Global-Health-Engineering/plastic-scanner/Images/initial_UI.jpeg

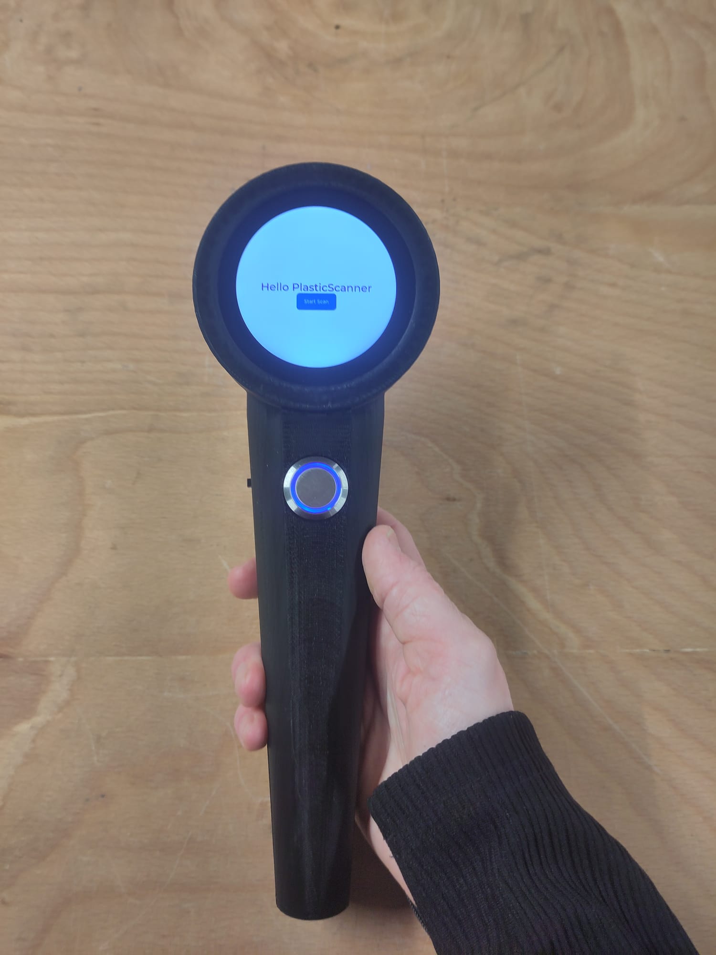
Images/initial_UI.jpeg
