Global-Health-Engineering/plastic-scanner/Images/scanning.jpeg

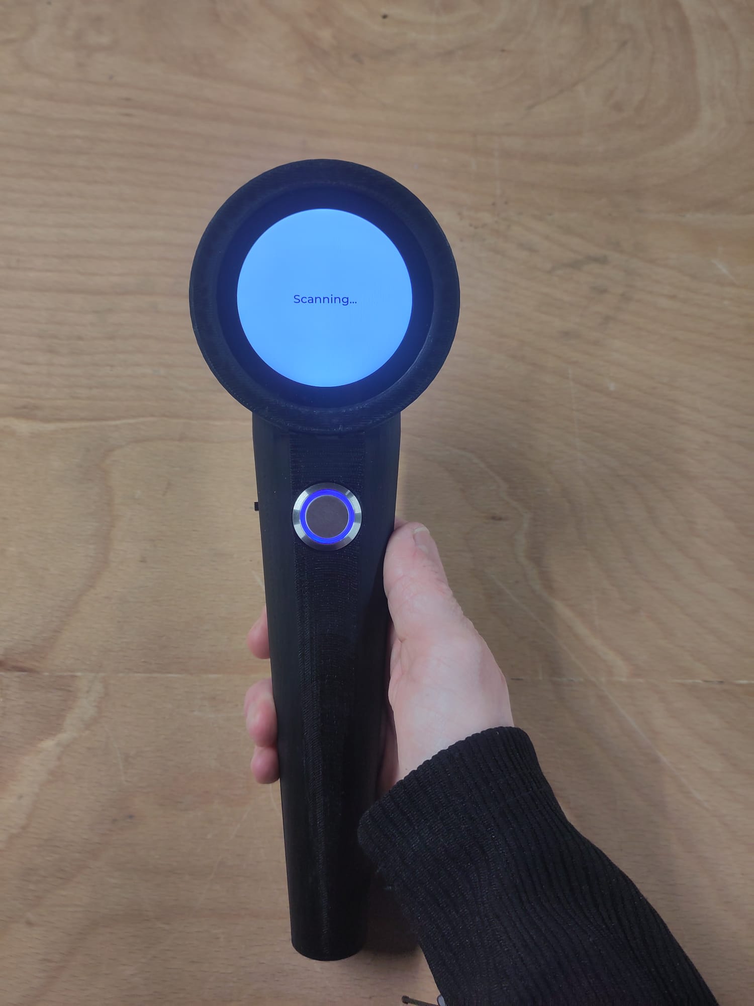
Images/scanning.jpeg
