Global-Health-Engineering/plastic-scanner/Images/WhatsApp Image 2026-01-21 at 16.56.18.jpeg

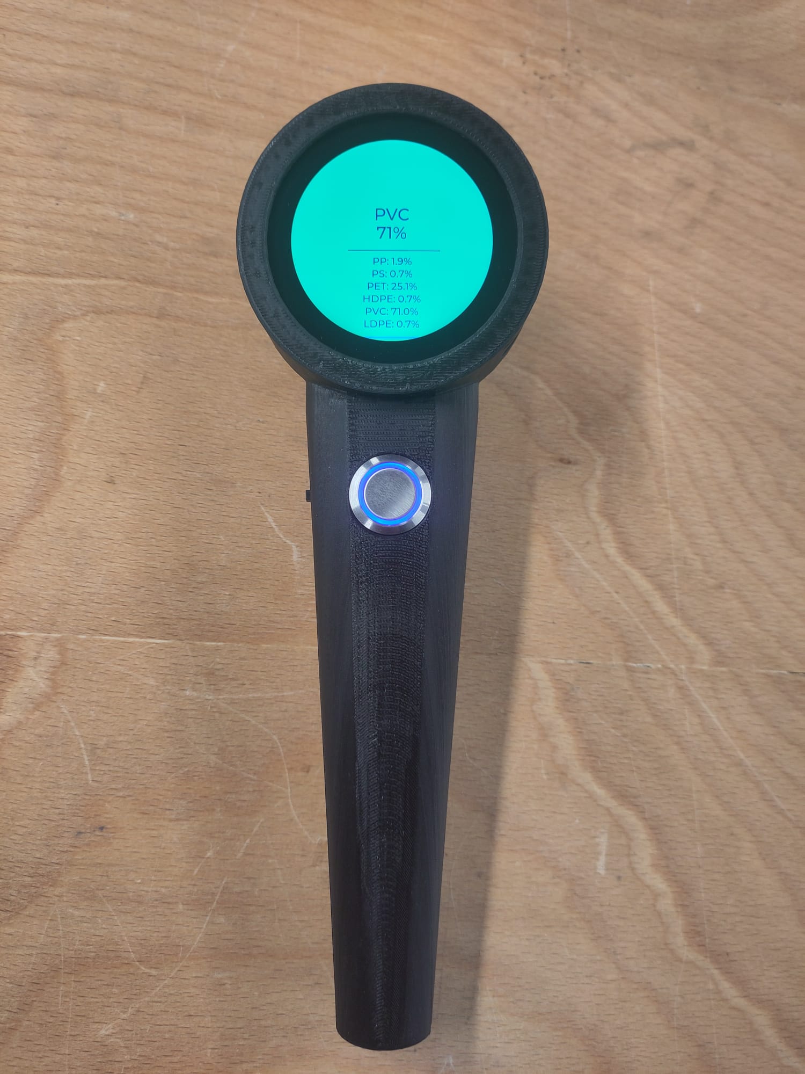
Images/WhatsApp Image 2026-01-21 at 16.56.18.jpeg
