Global-Health-Engineering/plastic-scanner/CAD/STEP files/low_shell_angle.STEP

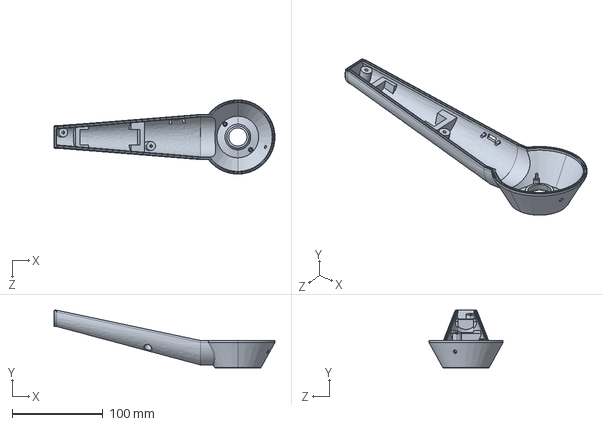
[picture p45: CAD file, 2026-01-22]
CAD/STEP files/low_shell_angle.STEP
244.0 x 63.5 x 82.0 mm
