Global-Health-Engineering/plastic-scanner/CAD/STEP files/fixture_LCD.STEP

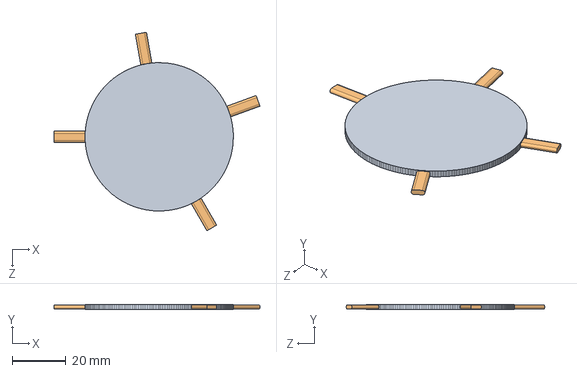
[picture p46: CAD file, 2026-01-22]
CAD/STEP files/fixture_LCD.STEP
76.4 x 2.00 x 73.6 mm
