Global-Health-Engineering/plastic-scanner/Hardware/Scanning PCB/RoundScanner_Ki_CAD_files/3dmodels/Diodes_Inc._-_BSS138DW-7-F 2.step

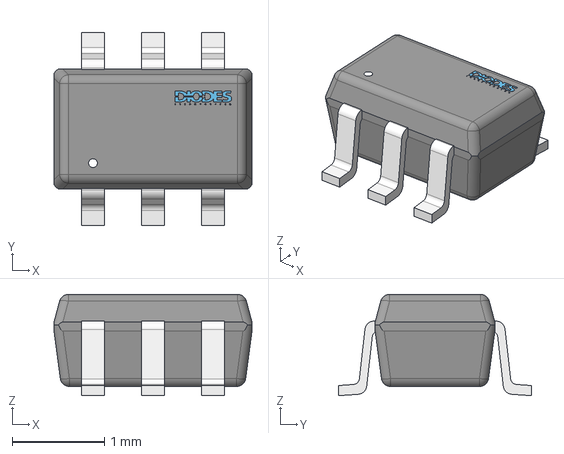
[picture p47: CAD file, 2026-01-18]
Hardware/Scanning PCB/RoundScanner_Ki_CAD_files/3dmodels/Diodes_Inc._-_BSS138DW-7-F 2.step
2.15 x 2.10 x 1.10 mm
