Global-Health-Engineering/plastic-scanner/Firmware/Firmware Handheld Plastic Scanner LilyGo/dimensions/T-RGB-PCB.DXF

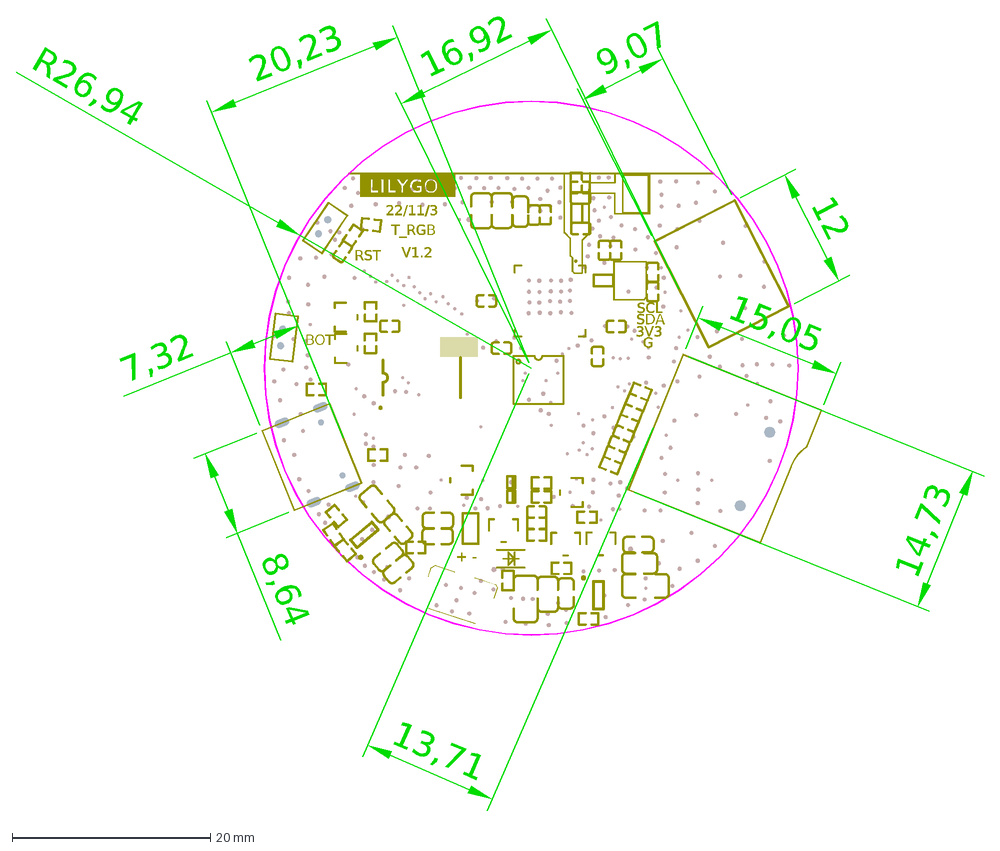
[picture p48: CAD file, 2026-01-21]
Firmware/Firmware Handheld Plastic Scanner LilyGo/dimensions/T-RGB-PCB.DXF
22/11/3
V1.2
T_RGB
3V3
SDA
SCL
G
-
+
BOT
RST
R26,94
13,71
20,23
16,92
12
9,07
15,05
14,73
8,64
7,32
