Global-Health-Engineering/plastic-scanner/Hardware/Scanning PCB/RoundScanner_Ki_CAD_files/3dmodels/OPA2376AID.stp

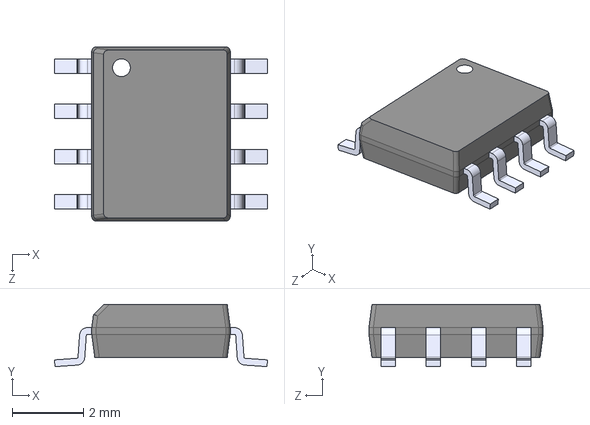
[picture p49: CAD file, 2026-01-18]
Hardware/Scanning PCB/RoundScanner_Ki_CAD_files/3dmodels/OPA2376AID.stp
5.99 x 1.75 x 4.90 mm
