Global-Health-Engineering/plastic-scanner/Hardware/Scanning PCB/RoundScanner_Ki_CAD_files/3dmodels/AP7312-1833W6-7.stp

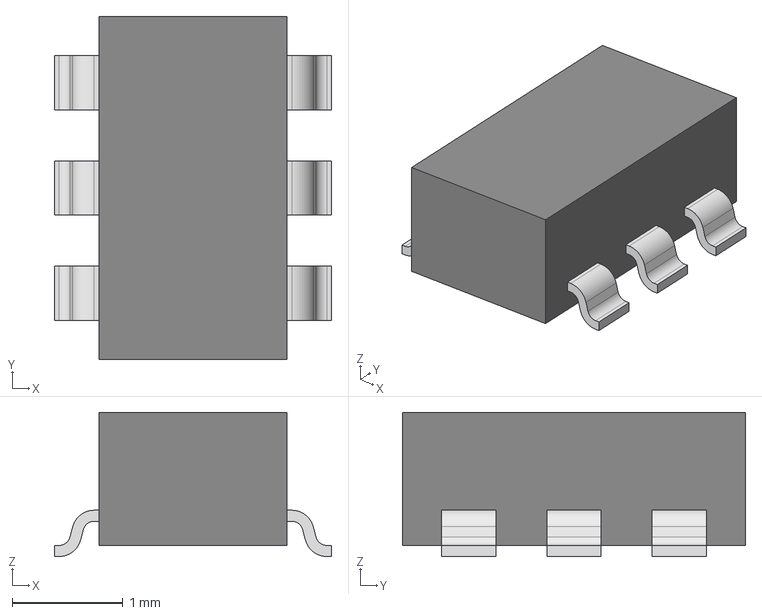
[picture p50: CAD file, 2026-01-18]
Hardware/Scanning PCB/RoundScanner_Ki_CAD_files/3dmodels/AP7312-1833W6-7.stp
2.50 x 3.10 x 1.30 mm
