Global-Health-Engineering/plastic-scanner/Hardware/Scanning PCB/RoundScanner_Ki_CAD_files/3dmodels/Everlight_-_EAHC2835WD6 2.step

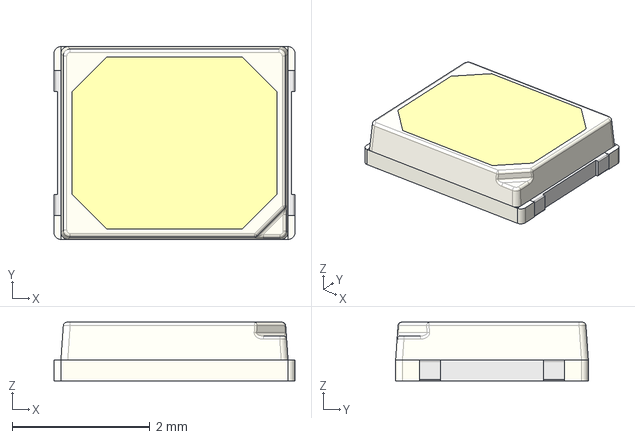
[picture p51: CAD file, 2026-01-18]
Hardware/Scanning PCB/RoundScanner_Ki_CAD_files/3dmodels/Everlight_-_EAHC2835WD6 2.step
3.50 x 2.80 x 0.85 mm
